Kautuk-Purohit/usb-c-3v3-sensor-breakout/Images/pcb_design/final_pcb_layout_DRC_report.png

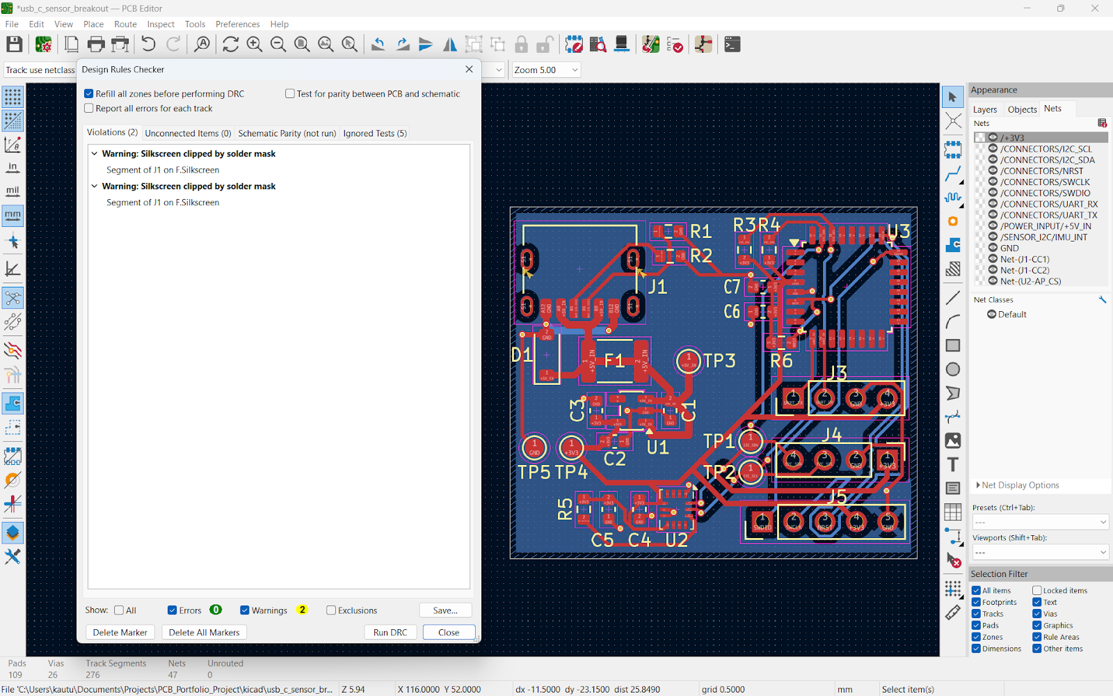
Images/pcb_design/final_pcb_layout_DRC_report.png
