Kautuk-Purohit/usb-c-3v3-sensor-breakout/Images/pcb_design/iteration1_traces_DRC_report.png

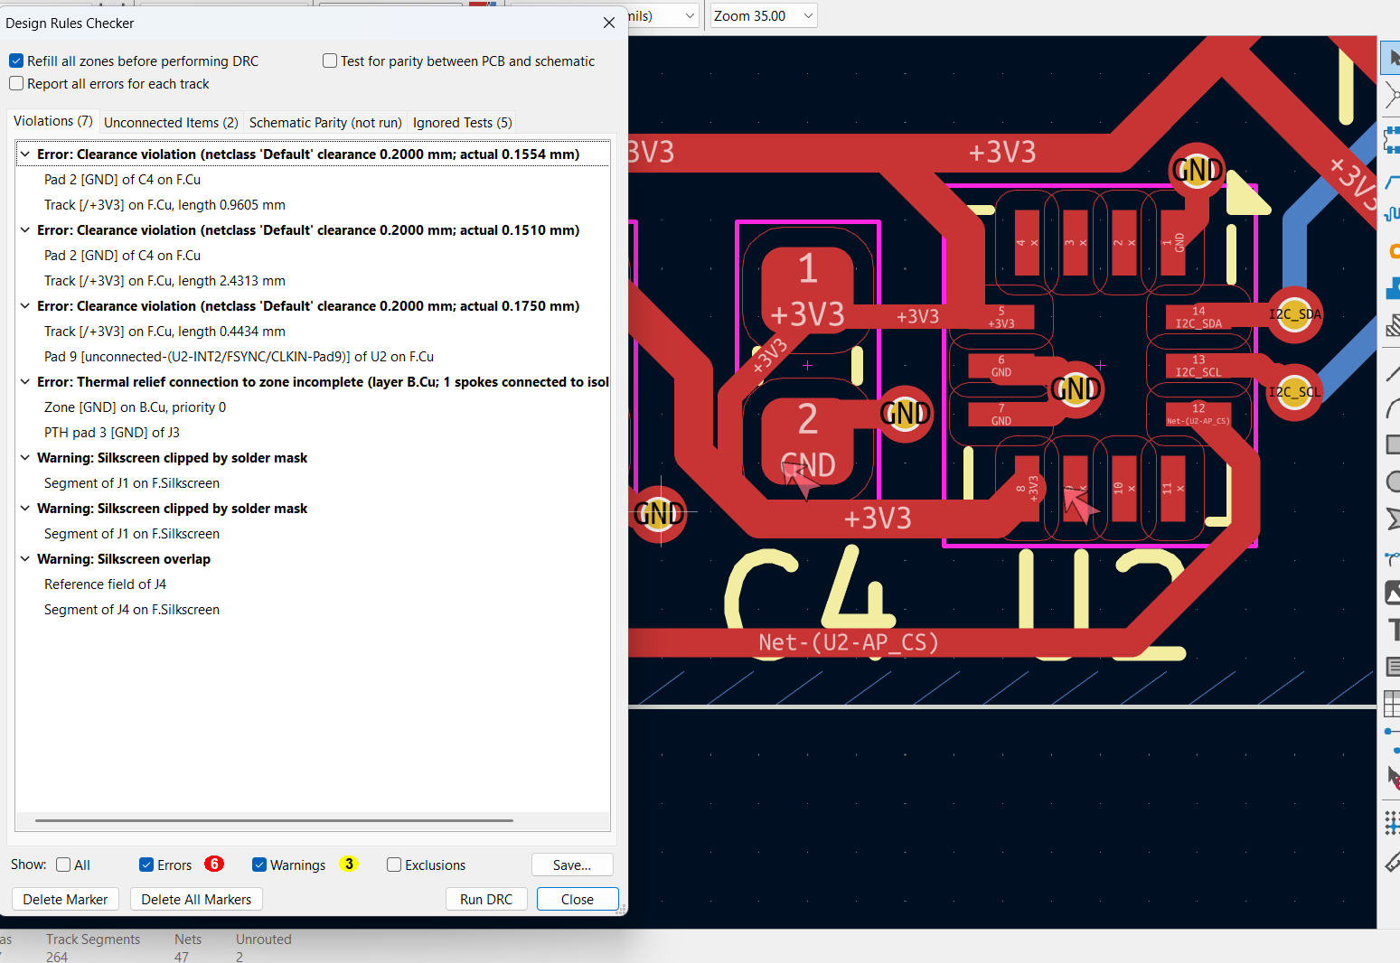
Images/pcb_design/iteration1_traces_DRC_report.png
