Kautuk-Purohit/usb-c-3v3-sensor-breakout/Images/schematic/assigned_footprints.png

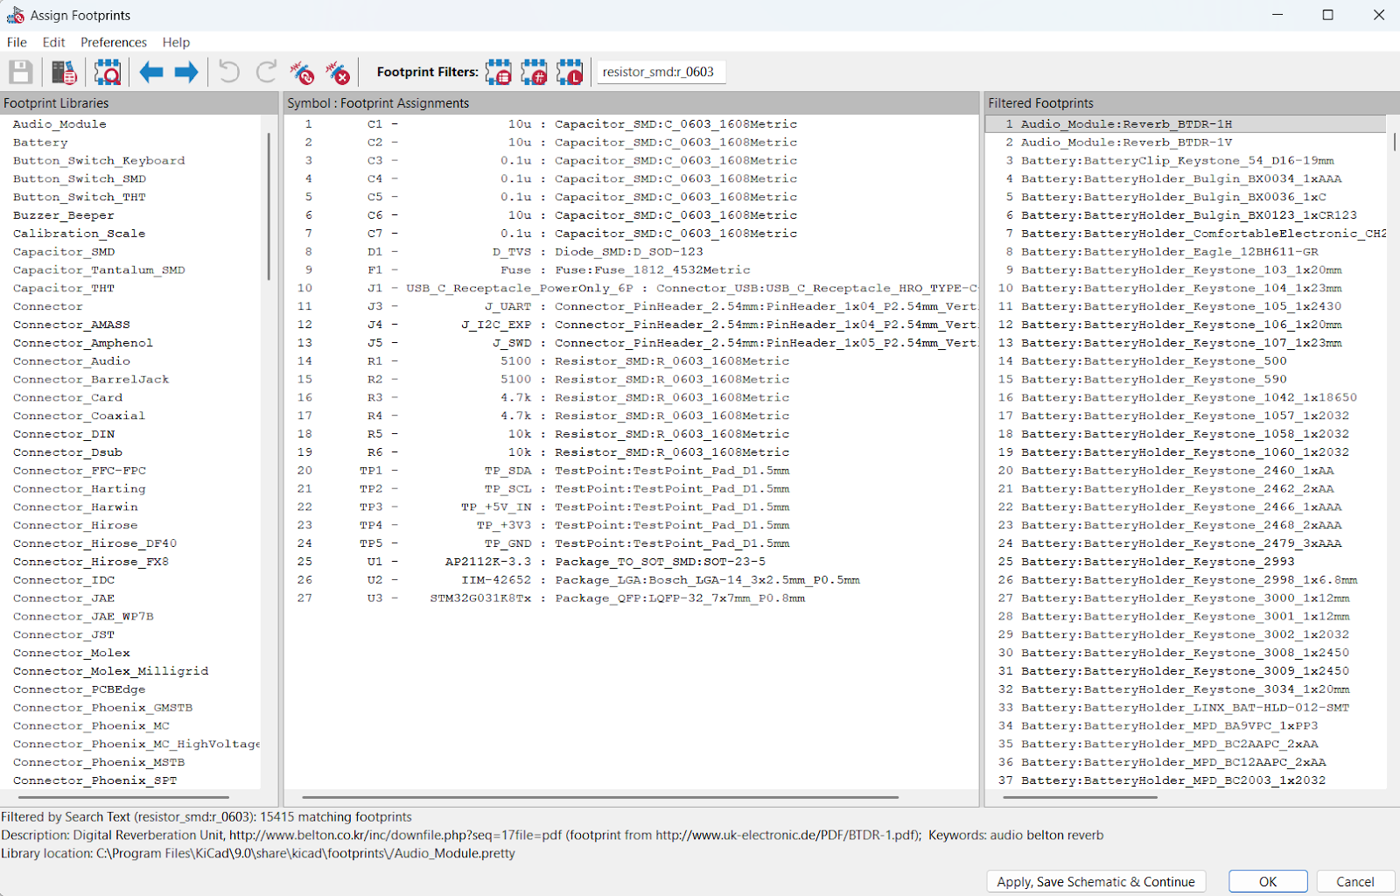
Images/schematic/assigned_footprints.png
