Kautuk-Purohit/usb-c-3v3-sensor-breakout/Images/schematic/connectors_iteration1.png

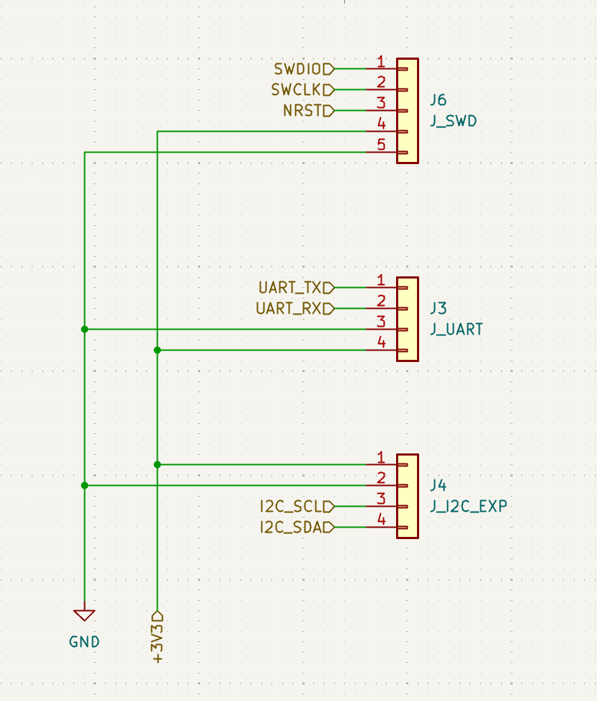
Images/schematic/connectors_iteration1.png
