Kautuk-Purohit/usb-c-3v3-sensor-breakout/Images/schematic/final_connectors_schematic.png

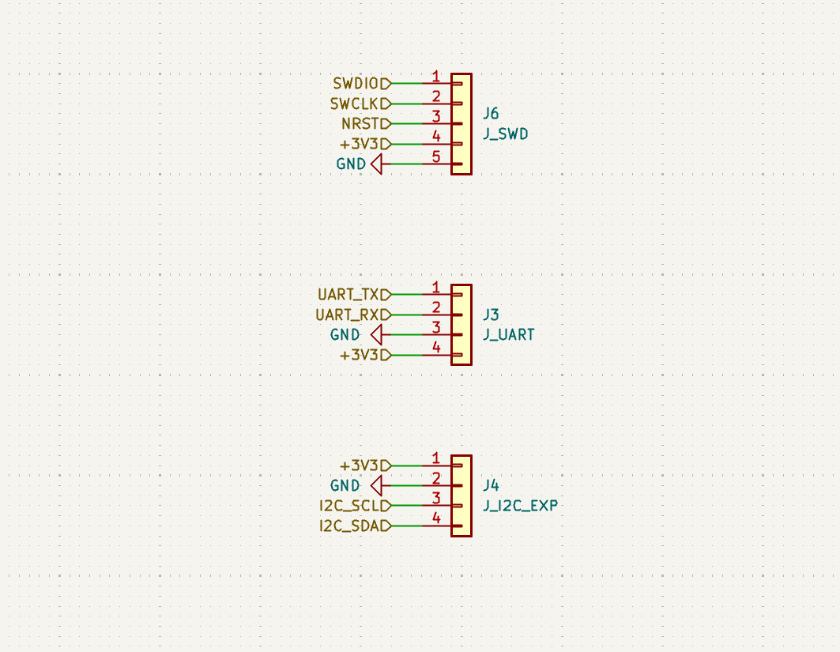
Images/schematic/final_connectors_schematic.png
