Kautuk-Purohit/usb-c-3v3-sensor-breakout/Images/schematic/final_MCU_schematic.png

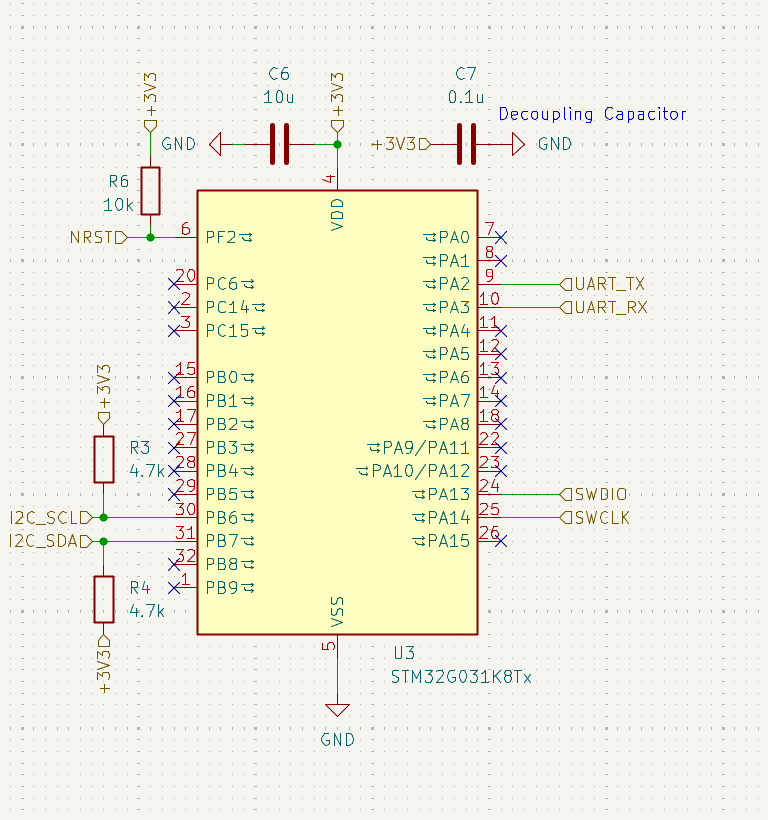
Images/schematic/final_MCU_schematic.png
