Kautuk-Purohit/usb-c-3v3-sensor-breakout/Images/schematic/final_power_input_schematic.png

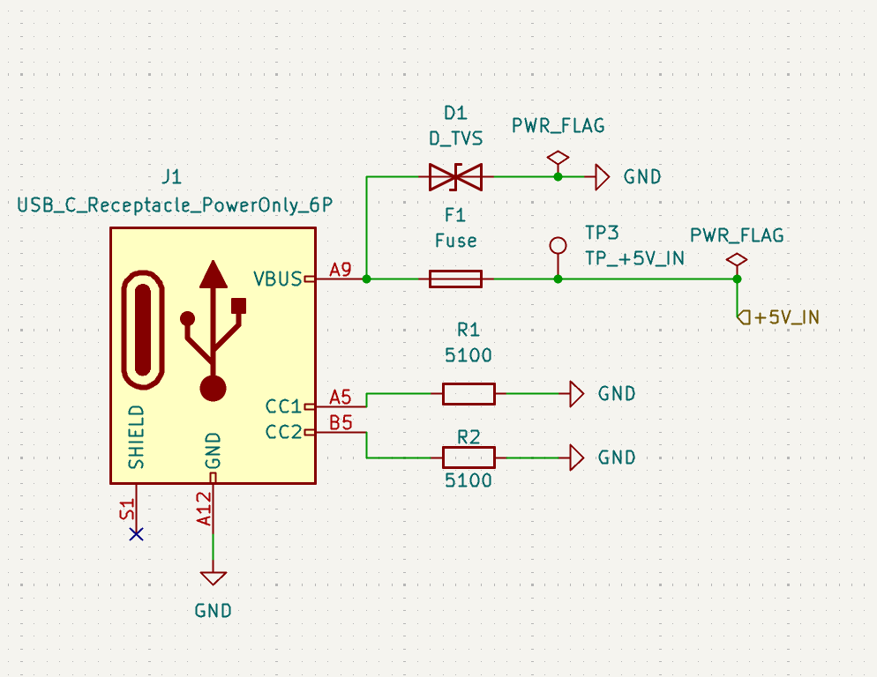
Images/schematic/final_power_input_schematic.png
