Kautuk-Purohit/usb-c-3v3-sensor-breakout/Images/schematic/final_top_page_schematic.png

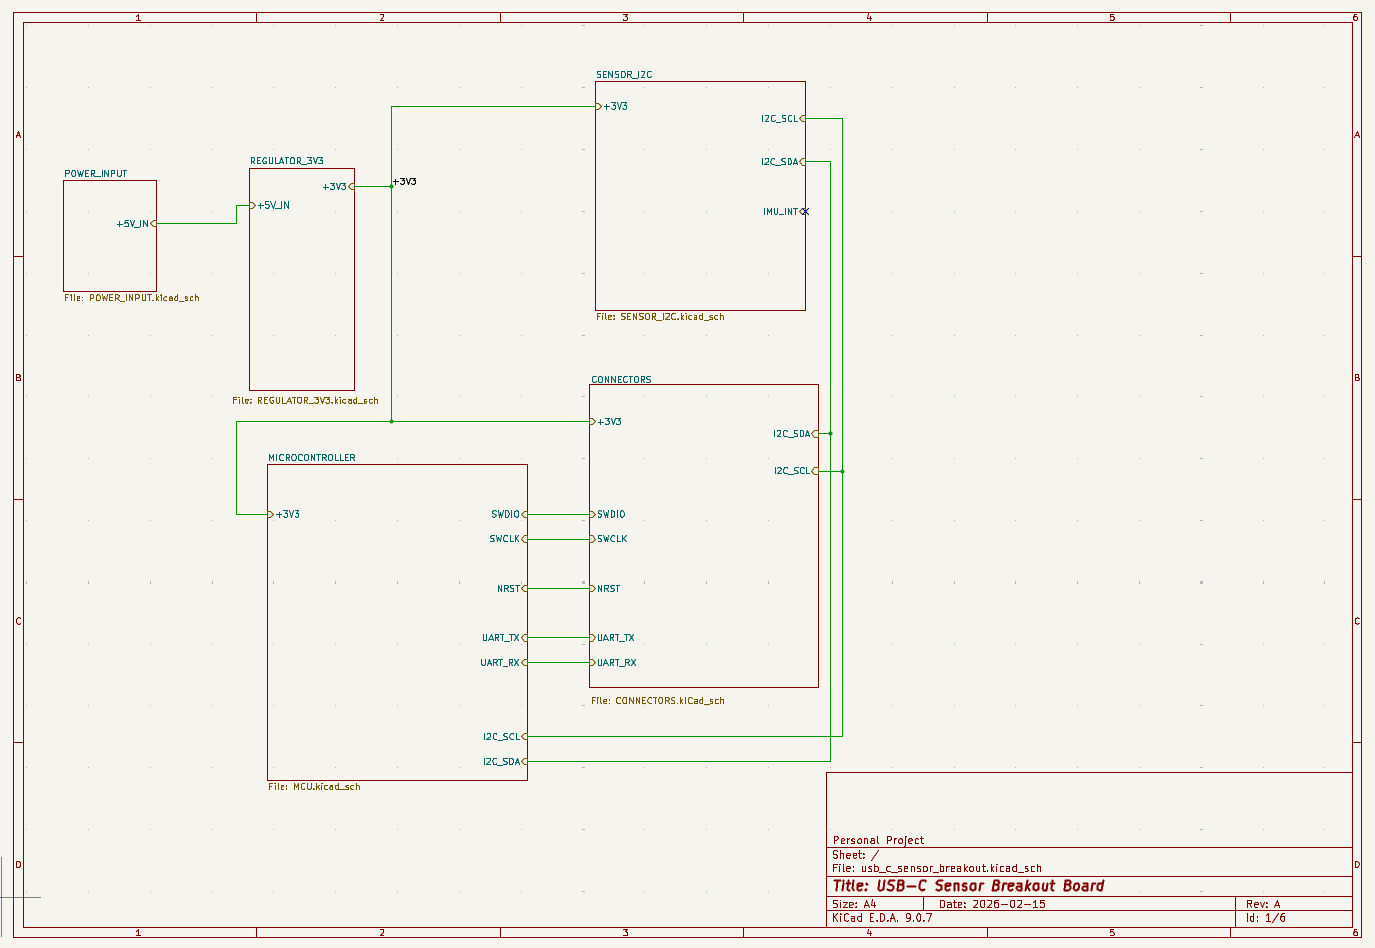
Images/schematic/final_top_page_schematic.png
