Kautuk-Purohit/usb-c-3v3-sensor-breakout/Images/schematic/regulator_iteration2.png

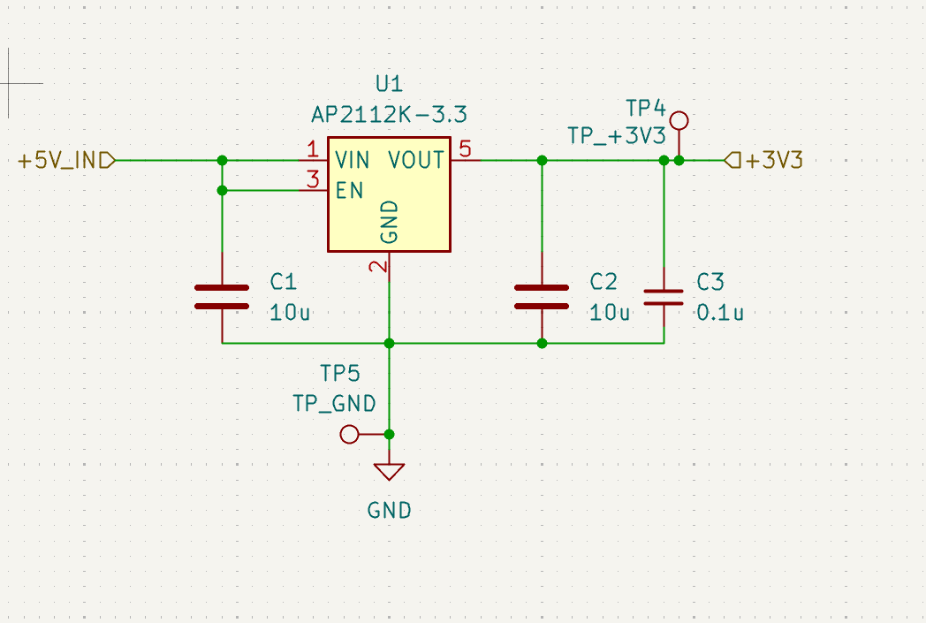
Images/schematic/regulator_iteration2.png
