Kautuk-Purohit/usb-c-3v3-sensor-breakout/Images/schematic/sensor_iteration2.png

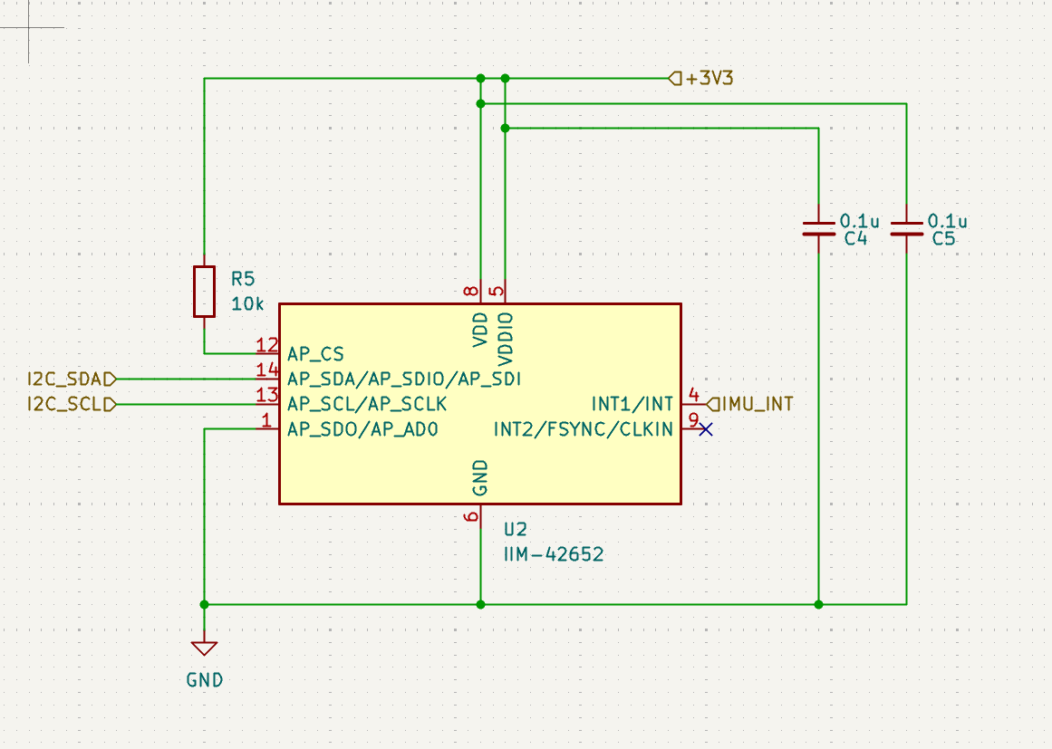
Images/schematic/sensor_iteration2.png
