Kautuk-Purohit/usb-c-3v3-sensor-breakout/Images/schematic/top_level_iteration2.png

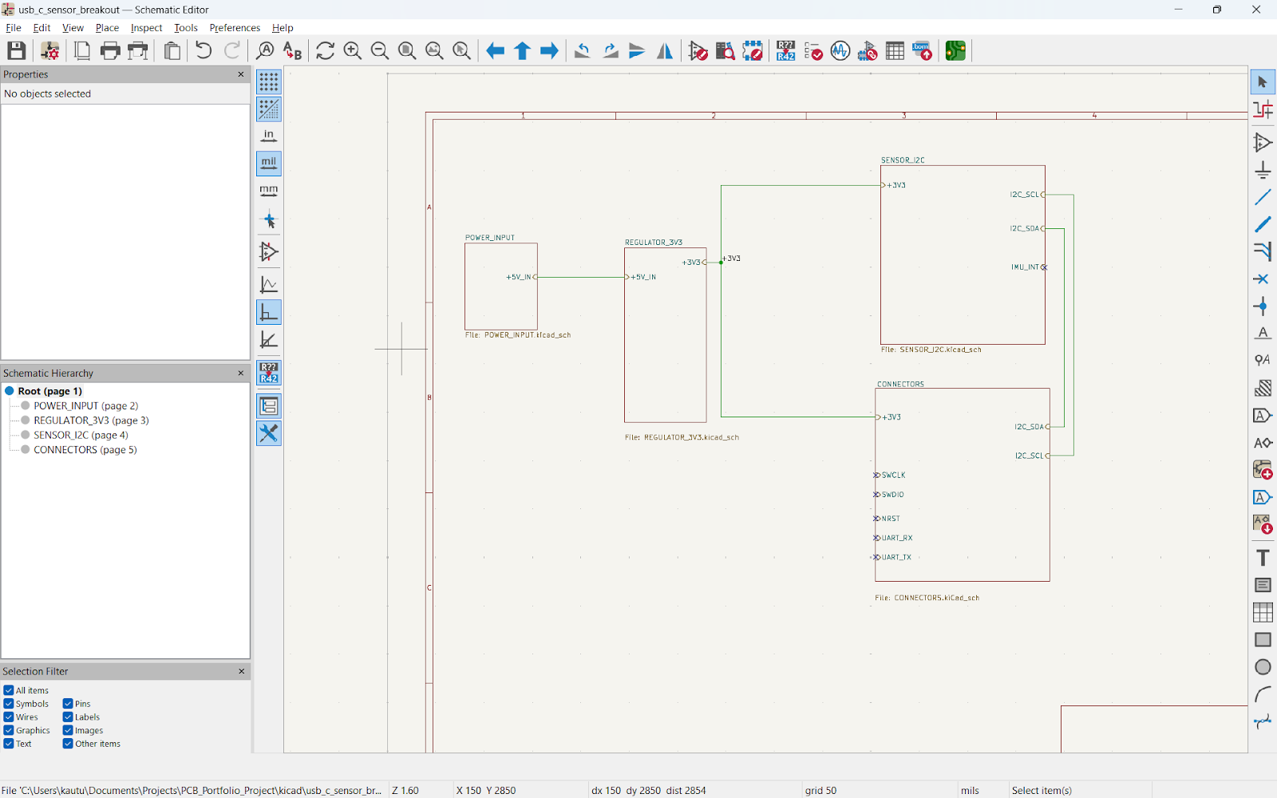
Images/schematic/top_level_iteration2.png
