Kautuk-Purohit/usb-c-3v3-sensor-breakout/Images/pcb_design/final_component_layout.png

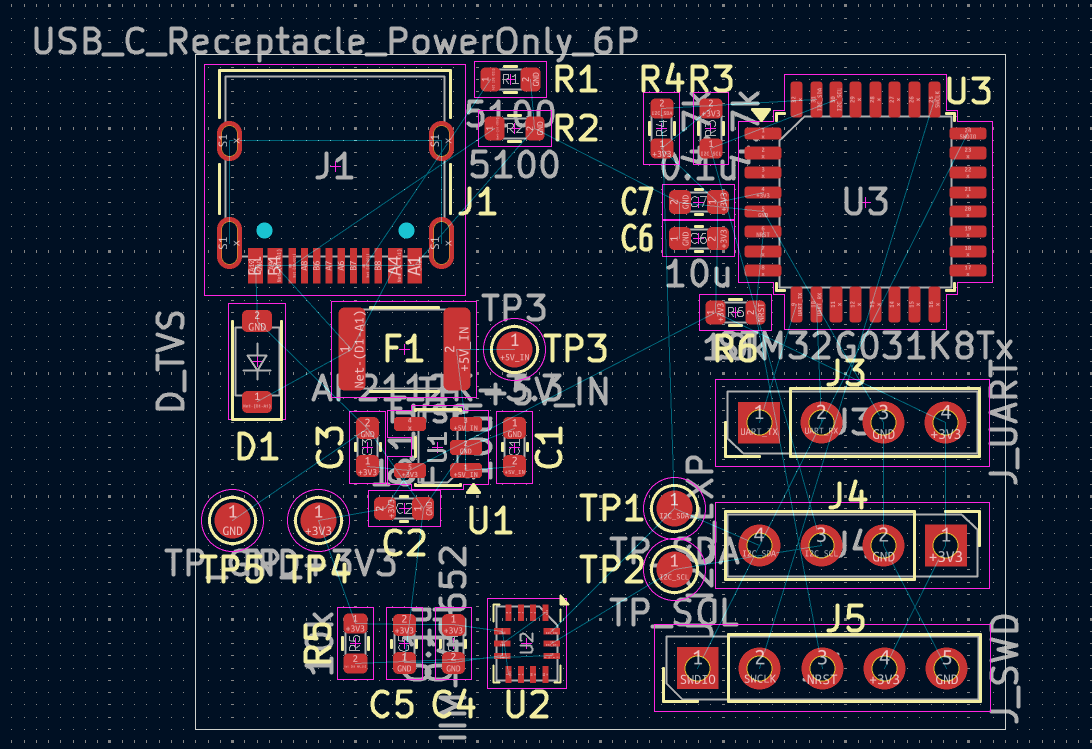
Images/pcb_design/final_component_layout.png
