Kautuk-Purohit/usb-c-3v3-sensor-breakout/Images/manufacturing/drill_settings.png

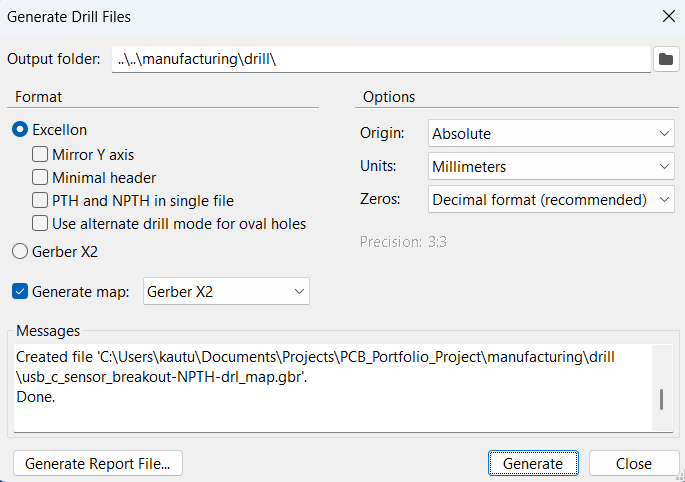
Images/manufacturing/drill_settings.png
