Kautuk-Purohit/usb-c-3v3-sensor-breakout/Images/manufacturing/gerber_settings.png

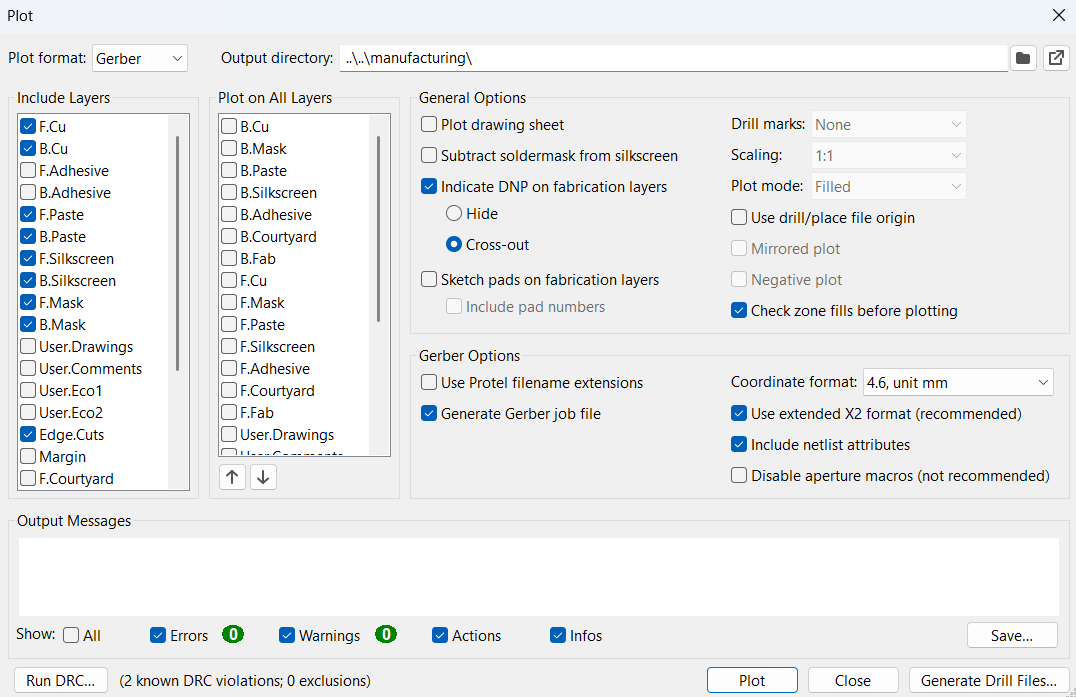
Images/manufacturing/gerber_settings.png
