Kautuk-Purohit/usb-c-3v3-sensor-breakout/Images/manufacturing/placement_settings.png

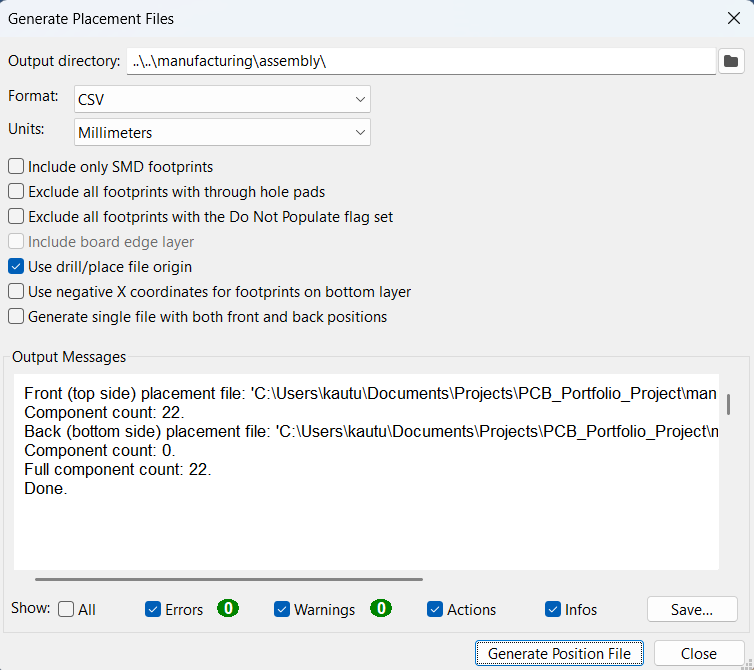
Images/manufacturing/placement_settings.png
